pts211/LiteBrite/Processing/ProcessingController/animated/coffee_crop_invert.gif

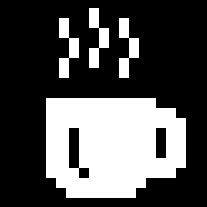
Processing/ProcessingController/animated/coffee_crop_invert.gif
