pts211/LiteBrite/Processing/ProcessingController/animated/coffee_crop_invert_wide.gif

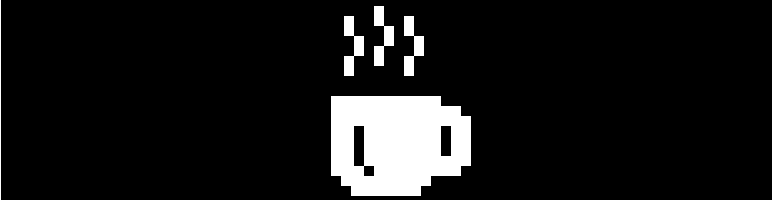
Processing/ProcessingController/animated/coffee_crop_invert_wide.gif
