pts211/LiteBrite/Processing/ProcessingController/images/blinky-animation-crop.gif

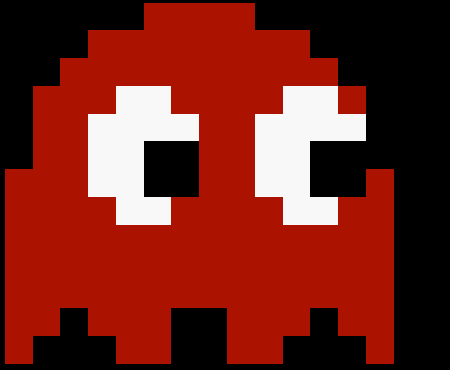
Processing/ProcessingController/images/blinky-animation-crop.gif
