pts211/LiteBrite/Processing/ProcessingController/images/pokeball.png

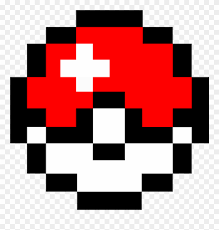
Processing/ProcessingController/images/pokeball.png
