pts211/LiteBrite/Processing/ProcessingController/PegGrid.pde

public class PegGrid
{
  final static boolean staggered = false;
  final static int GRID_W = 38;
  final static int GRID_H = 24;

  final int DIAMETER = width/GRID_W;

  PApplet parent;
  OPC opc;
  String ip = "127.0.0.1";
  int port = 7890;

  Point brushPeg;

  Peg[] pegs = new Peg[GRID_W*GRID_H];

  PegGrid(PApplet parent, String ip, int port) {
    this.parent = parent;
    this.ip = ip;
    this.port = port;

    this.brushPeg = new Point(0, 0); //Defaulting brush peg to top right of the board.

    //parent.registerDraw(this);

    opc = new OPC(parent, ip, port);
    opc.showLocations(false);

    generateGrid();
    //opc.ledGrid(0, 38, 24, width/2.0, height/2.0, DIAMETER, DIAMETER, 0, false);

    for (int i = 0; i < pegs.length; i++) {
      Point p = opc.getLocationByIndex(i);
      pegs[i] = new Peg(p, int(DIAMETER*0.9));
      //println("peg[" + i + "]: ( " + pegs[i].getX() + ", " + pegs[i].getY() + " )");
    }
  }

  void setBrushPeg(int x, int y)
  {
    this.brushPeg = new Point(x, y);
  }

  void nextBrushPegColor()
  {
    int idx = getIndexAtPoint(brushPeg.getX(), brushPeg.getY());
    pegs[idx].nextColor();
    config.paintColor = pegs[idx].getColor();
    println("setting brush peg");
    resetBrushes();
  }

  color getBrushPegColor()
  {
    return getColorAtCoord(brushPeg.getX(), brushPeg.getY());
  }
  
  Peg getPegAtCoord(int x, int y)
  {
    return pegs[getIndexAtPoint(x,y)];
  }

  boolean isBrushPeg(int idx)
  {
    if( idx == getIndexAtPoint(brushPeg.getX(),brushPeg.getY()) )
    {
     return true; 
    }
    return false;
  }

  boolean isBrushPeg(int x, int y)
  {
    if (brushPeg.getX() == x && brushPeg.getY() == y) {
      return true;
    }
    return false;
  }

  void resetBrushes()
  {
    for (int i = 0; i < pegs.length; i++) {
      pegs[i].resetBrush();
    }
  }

  private void generateGrid()
  { 
    int index = 0;
    int stripLength = GRID_W;
    int numStrips = GRID_H;
    float x = width/2.0;
    float y = height/2.0;
    float ledSpacing = DIAMETER;
    float stripSpacing = DIAMETER;
    float angle = 0;
    boolean zigzag = true;
    boolean reversed = false;

    float s = sin(angle + HALF_PI);
    float c = cos(angle + HALF_PI);
    for (int i = 0; i < numStrips; i++) {
      //reversed = ((i % 2) == 1); //Use if alternating every row.

      if ( i % 8 == 0) {
        reversed = !reversed;
      }
      /*
      //Use if alternating FadeCandy's on different sides.
       if( (i != 0) && ((i % 8) == 0) ){
       reversed = !reversed; 
       }
       */

      if (staggered) {
        opc.ledStrip(index + stripLength * i, stripLength, 
          (x + (i - (numStrips-1)/2.0) * stripSpacing * c) + (reversed?(DIAMETER/2):0), 
          (y + (i - (numStrips-1)/2.0) * stripSpacing * s), 
          ledSpacing, 
          angle, zigzag && reversed);
      } else {
        opc.ledStrip(index + stripLength * i, stripLength, 
          (x + (i - (numStrips-1)/2.0) * stripSpacing * c), 
          (y + (i - (numStrips-1)/2.0) * stripSpacing * s), 
          ledSpacing, 
          angle, zigzag && reversed);
      }
    }
  }

  /* ******************** COLOR FUNCTIONS ******************** */

  public void nextColorAtCoord(int xpos, int ypos)
  {
    int idx = getIndexAtPoint(xpos, ypos);
    nextColorAtIdx(idx);
  }

  public color getColorAtCoord(int xpos, int ypos)
  {
    println("xpos: " + xpos + " ypos: " + ypos);
    int idx = getIndexAtPoint(xpos, ypos);
    return pegs[idx].getColor();
  }

  public void setColorAtCoord(int xpos, int ypos, color c)
  {
    int idx = getIndexAtPoint(xpos, ypos);
    pegs[idx].setColor(c);
  }

  public void nextColorAtIdx(int idx)
  {
    if (config.usePaintColor) {
      pegs[idx].nextColorBrush();
    } else {
      pegs[idx].nextColor();
    }
  }

  public void setAll(int c)  
  {
    for (int i = 0; i < pegs.length; i++) {
      pegs[i].setColor(c);
    }
  }

  public void setRow(int row, int c)
  {
    for (int i = 0; i < GRID_W; i++) {
      int idx = getIndexAtPoint(i, row);
      pegs[idx].setColor(c);
    }
  }

  public void setCol(int col, int c)
  {
    for (int i = 0; i < GRID_W; i++) {
      int idx = getIndexAtPoint(col, i);
      pegs[idx].setColor(c);
    }
  }

  public void setAllBrightness(int b)
  {
    for (int i = 0; i < pegs.length; i++) {
      pegs[i].setBrigthness(b);
    }
  }

  public void setAllOff()
  {
    setAll(Colors.BLACK);
  }

  public void setAllRandom()
  {
    for (int i = 0; i < pegs.length; i++) {
      color c = color(random(0, 255), random(0, 255), random(0, 255));
      pegs[i].setColor(c);
    }
  }

  public void setAllRandomStandard()
  {
    for (int i = 0; i < pegs.length; i++) {
      pegs[i].setColor(Colors.randomColor());
    }
  }

  public void loadImg()
  {
    loadPixels();

    for (int i = 0; i < pegs.length; i++) {
      int pixelLocation = opc.getLocationByIndexAsInt(i);
      int pixel = pixels[pixelLocation];
      pegs[i].setColor(pixel);
    }
    updatePixels();
  }
  /*
  public void saveImg()
   {
   loadPixels();
   
   for (int i = 0; i < pegs.length; i++) {
   int pixelLocation = opc.getLocationByIndexAsInt(i);
   int pixel = pixels[pixelLocation];
   pegs[i].setColor(pixel);
   }
   updatePixels();
   }
   */
  /*
  //TODO REMOVE - Testing loading an image into an off-screen object to prevent
   //possible flickering. 
   public void loadImg(PImage img)
   {
   img.loadPixels();
   
   for (int i = 0; i < pegs.length; i++) {
   int pixelLocation = opc.getLocationByIndexAsInt(i);
   int pixel = img.pixels[pixelLocation];
   pegs[i].setColor(pixel);
   }
   img.updatePixels();
   }
   */

  public Peg[] getPegs()
  {
    return this.pegs;
  }

  public void draw()
  {
    pushMatrix();
    pushStyle();
    for (int i = 0; i < pegs.length; i++) {
      pegs[i].draw();
    }
    popMatrix();
    popStyle();
  }

  public Peg mousePressed(int xpos, int ypos)
  { 
    Point mP = new Point(mouseX, mouseY);
    for (int i = 0; i < pegs.length; i++) {
      Point pP = pegs[i].getPoint();

      if (containmentCheck(mP, pP, DIAMETER/2)) {
        println("Clicked peg " + i + "."); 
        if ( isBrushPeg(i) ) {
          println("Mouse clicked brush");
          nextBrushPegColor();
        } else if (config.usePaintColor) {
          pegs[i].nextColorBrush();
        } else {
          pegs[i].nextColor();
        }

        return pegs[i];
      }
    }
    return null;
  }

  private boolean containmentCheck(Point p1, Point p2, int radius)
  {
    //if d^2 <= r^2 we're in the circle. Via Pythagorean theorem
    //d^2 = (p1.x - p2.x)^2 + (p1.y - p2.y)^2 

    int px = (p1.getX() - p2.getX());
    int py = (p1.getY() - p2.getY());

    int r2 = radius*radius;
    int d2 = (px*px) + (py*py);

    if (d2 <= r2) {
      return true;
    }
    return false;
  } 

  public int getIndexAtPoint(int x, int y)
  {
    //println("getting point at ( " + x + ", " + y + ")");
    if ( (x < GRID_W) && (y < GRID_H) ) {
      return (((y % 2) == 1)? (GRID_W -1 - x) : x) + GRID_W * y;
    }
    return -1;
  }
}
